WhoTheHeck/GoPlusExtender/LTSpice_LED-PWM-simulation.asc

C2: cap; 47n
C4: cap; 47n
C5: cap; 47n
D3: diode; 1N914
D4: schottky; RB481Y
D5: schottky; RB481Y
D6: schottky; RB481Y
R4: res; 1k
R5: res; 82k
R6: res; 10k
R7: res; 1k
R9: res; 82k
R10: res; 1R
R11: res; 220R
R12: res; 10k
V3: voltage; PULSE(0 4.1 0 0 0 40m 1)
V4: voltage; PULSE(0 3.4V 10m 0 0 10u 250u 50)
V5: voltage; PULSE(0 3.4V 10m 0 0 250u 250u 50)
V6: voltage; 1.6V
V7: voltage; 1.2V
Named nets: 0, annode, 4%, 100%
.tran 60m
